jimmo/cpld-cpu/gateware/mem_page/mem_page.ucf

net data<0> loc=pin39;
net data<1> loc=pin40;
net data<2> loc=pin41;
net data<3> loc=pin42;
net data<4> loc=pin5;
net data<5> loc=pin6;
net data<6> loc=pin7;
net data<7> loc=pin8;

net addr<0> loc=pin12;
net addr<1> loc=pin13;
net addr<2> loc=pin14;
net addr<3> loc=pin16;
net addr<4> loc=pin18;
net addr<5> loc=pin19;
net addr<6> loc=pin20;
net addr<7> loc=pin21;
net addr<8> loc=pin22;
net addr<9> loc=pin23;
net addr<10> loc=pin27;
net addr<11> loc=pin28;
net addr<12> loc=pin29;

net output<0> loc=pin31;
net output<1> loc=pin32;
net output<2> loc=pin34;
net output<3> loc=pin36;
net output<4> loc=pin37;
net output<5> loc=pin38;

net z loc=pin30;

net nwe loc=pin43;
net nrst loc=pin33;

net prog_clk loc=p1;
net prog_data loc=p2;
net prog_latch loc=p3;
