jimmo/cpld-cpu/gateware/decoder/decoder.vhd

library ieee;
use ieee.std_logic_1164.all;
use ieee.numeric_std.all;

entity decoder is
  port (
  instr: in std_logic_vector(2 downto 0);
  state: out std_logic_vector(2 downto 0);
  ram_oe: out std_logic;
  ram_we: out std_logic;
  pc_oe: out std_logic;
  pc_we: out std_logic;
  alu_oe: out std_logic;
  alu_we: out std_logic;
  a_oe: out std_logic;
  a_we: out std_logic;
  x_oe: out std_logic;
  x_we: out std_logic;
  ir_oe: out std_logic;
  ir_we: out std_logic;
  ar_oe: out std_logic;
  ar_we: out std_logic;

  pc_inc: out std_logic;
  idx_en: out std_logic;

  z: in std_logic;
  carry: in std_logic;

  cc: out std_logic;

  clk: in std_logic;
  nrst: in std_logic
  );
end decoder;

architecture arch of decoder is
  signal s: unsigned(2 downto 0);
  signal carry_buf: std_logic := '0';
  signal z_buf: std_logic := '0';
begin
  process(nrst, clk)
  begin
    if (nrst = '0') then
      s <= "000";
    elsif rising_edge(clk) then
      s <= s + 1;
      carry_buf <= carry;
      z_buf <= z;
    end if;
  end process;

  state <= std_logic_vector(s);

  -- Ops:
  -- 000  nor a   (A)
  -- 001  add a   (A)
  -- 010  sta     (S)
  -- 011  jcc     (J)
  -- 100  nor x   (A)
  -- 101  add x   (A)
  -- 110  stx     (S)
  -- 111  jnz     (J)

  -- States     0    1    2    3    4    5    6    7
  -- RAM OE     X    X    X    X    A    A
  -- RAM WE                                   S          (Store A or X to RAM)
  -- IR OE                          X    X    X    X
  -- IR WE           X                                   (Load first byte of instr)
  -- AR OE                          X    X    X    X
  -- AR WE                     X                         (Load second byte of instr)
  -- PC INC               X         X
  -- ALU OE     X    X    X    X    X    X    X    X
  -- ALU WE                              A               (Store A/X + Data)
  -- A OE                                Sa   Sa
  -- A WE                                     Aa         (Load A from ALU)
  -- X OE                                Sx   Sx
  -- X WE                                     Ax         (Load X from ALU)
  -- IDX EN                         ASa  ASa  ASa  ASa
  -- PC WE                               J               (Set PC to IR/AR)
  -- CC                                  J               (Clear carry on A)

  ram_oe <= '0' when nrst = '1' and (s <= 3 or ((instr = "000" or instr = "001" or instr = "100" or instr = "101") and s <= 5)) else '1';

  ar_oe <= '0' when nrst = '1' and s > 3 else '1';
  ir_oe <= '0' when nrst = '1' and s > 3 else '1';
  pc_oe <= '0' when nrst = '1' and s <= 3 else '1';
  pc_inc <= '1' when nrst = '1' and (s = 2 or s = 4) else '0';

  ir_we <= '0' when nrst = '1' and s = 1 else '1';
  ar_we <= '0' when nrst = '1' and s = 3 else '1';

  -- alu
  alu_we <= '0' when nrst = '1' and (instr = "000" or instr = "001" or instr = "100" or instr = "101") and s = 5 else '1';
  alu_oe <= '0' when nrst = '1' else '1';
  --alu_oe <= '0' when (instr = "000" or instr = "001" or instr = "100" or instr = "101") and (s = 5 or s = 6) else '1';
  a_we <= '0' when nrst = '1' and (instr = "000" or instr = "001") and s = 6 else '1';
  x_we <= '0' when nrst = '1' and (instr = "100" or instr = "101") and s = 6 else '1';

  -- sta/stx
  a_oe <= '0' when nrst = '1' and instr = "010" and (s = 5 or s = 6) else '1';
  x_oe <= '0' when nrst = '1' and instr = "110" and (s = 5 or s = 6) else '1';

  process(instr, s)
  begin
    if nrst = '0' then
      ram_we <= 'Z';
    elsif (instr = "010" or instr = "110") and s = 6 then
      ram_we <= '0';
    else
      ram_we <= '1';
    end if;
  end process;

  -- Indexing for alu(a), sta
  idx_en <= '1' when nrst = '1' and (instr = "000" or instr = "001" or instr = "010") and s > 3 else '0';

  -- jcc c=0 / jnz z=0
  pc_we <= '0' when nrst = '1' and ((instr = "011" and carry_buf = '0') or (instr = "111" and z_buf = '0')) and s = 5 else '1';
  -- jcc c=1 / jnz z=1
  cc <= '1' when nrst = '1' and ((instr = "011" and carry_buf /= '0') or (instr = "111" and z_buf = '1')) and s = 5 else '0';
end arch;
